noise/modular-tap-handle/img/tap-top-apple.png

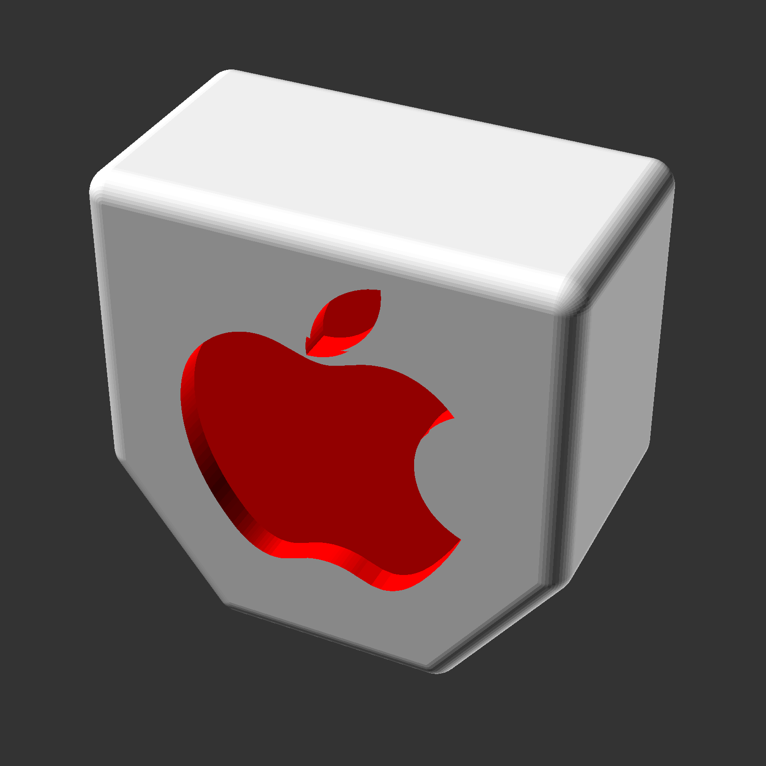
img/tap-top-apple.png
